heyjva/ergogen-keyboard/kicad/3d_models/Choc_V1_Hotswap.step

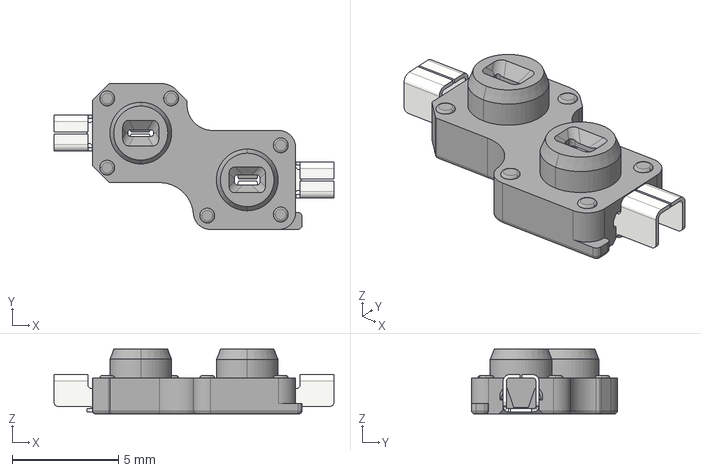
[picture p16: CAD file, 2026-08-23]
kicad/3d_models/Choc_V1_Hotswap.step
13.2 x 6.85 x 3.05 mm
